stefanhepp/fancylights/firmware/MainController/src/ProjectorController.cpp

/*
 * @project     FancyController
 * @author      Stefan Hepp, stefan@stefant.org
 *
 * LED intensity and mode implementation.
 *
 * Copyright 2024 Stefan Hepp
 * License: GPL v3
 * See 'COPYRIGHT.txt' for copyright and licensing information.
 */
#include "ProjectorController.h"

#include <functional>

// for EVERY_N_MILLIS macro
#include <FastLED.h>

#include <commands.h>

#include "config.h"

HardwareSerial projectorSerial(UART_PROJECTOR);

const char *TOPIC_PROJECTOR_MODE = "mode";
const char *TOPIC_PROJECTOR_MOVE = "move";
const char *TOPIC_SCREEN_MOVE = "screen";
const char *TOPIC_PROJECTOR_POWER = "power";
const char *TOPIC_PROJECTOR_SWITCH = "endstop";

ProjectorController::ProjectorController(Settings &settings, MqttClient &mqttClient)
: mSettings(settings), mMqttClient(mqttClient)
{
}

void ProjectorController::mqttCallback(const char *key, const char* payload, unsigned int length)
{
    if (length == 0) {
        return;
    }
    if (strcmp(key, TOPIC_PROJECTOR_MODE) == 0) {
        ProjectorCommand mode;
        if (parseProjectorCommand(payload, mode)) {
            sendMode(mode, false);
        }
    }
    if (strcmp(key, TOPIC_PROJECTOR_MOVE) == 0) {
        LiftCommand move;
        if (parseLiftCommand(payload, move)) {
            moveProjector(move);
        }
    }
    if (strcmp(key, TOPIC_SCREEN_MOVE) == 0) {
        LiftCommand move;
        if (parseLiftCommand(payload, move)) {
            moveScreen(move);
        }
    }
}

void ProjectorController::subscribeCallback()
{
    mMqttClient.subscribe(MQS_PROJECTOR, TOPIC_PROJECTOR_MODE);
    mMqttClient.subscribe(MQS_PROJECTOR, TOPIC_PROJECTOR_MOVE);
    mMqttClient.subscribe(MQS_PROJECTOR, TOPIC_SCREEN_MOVE);
}

bool ProjectorController::isPowerChanging()
{
    return mPowerChangeTime > 0 && (millis() - mPowerChangeTime) < 1000; 
}

void ProjectorController::sendMode(ProjectorCommand mode, bool publish)
{
    bool modeChange = (mMode != mode);
    
    if ((mMode == ProjectorCommand::PROJECTOR_OFF) != (mode == ProjectorCommand::PROJECTOR_OFF)) {
        mPowerChangeTime = millis();
    }

    mMode = mode;

    // send command via SW UART to projector
    projectorSerial.write(ProjectorOpcode::POP_MODE);
    projectorSerial.write(mode);

    if (modeChange && mModeChangeCallback) {
        mModeChangeCallback(mode);
    }

    if (publish) {
        mMqttClient.publish(MQS_PROJECTOR, TOPIC_PROJECTOR_MODE, strProjectorCommand(mode));
    }
}

void ProjectorController::moveProjector(LiftCommand direction)
{
    projectorSerial.write( direction == LiftCommand::LIFT_UP ? ProjectorOpcode::POP_LOCK : ProjectorOpcode::POP_UNLOCK );
}

void ProjectorController::moveScreen(LiftCommand direction)
{
    mCntPulse = 5;
    if (direction == LiftCommand::LIFT_UP || direction == LiftCommand::LIFT_STOP) {
        digitalWrite(PIN_SCREEN_UP, HIGH);
    }
    if (direction == LiftCommand::LIFT_DOWN || direction == LiftCommand::LIFT_STOP) {
        digitalWrite(PIN_SCREEN_DOWN, HIGH);
    }
}

void ProjectorController::requestStatus()
{
    // Request status from projector controller
    projectorSerial.write(ProjectorOpcode::POP_STATUS);

    if (isPowerChanging()) {
        mDelayedStatusRequest = true;
    }
}

void ProjectorController::processSerialData(uint8_t data)
{
    mCommandData[mBufferSize++] = data;

    switch (mCommandData[0]) {
        case ProjectorOpcode::POP_STATUS:
            if (mBufferSize >= 2) {
                bool hasPowerStatus = ((mCommandData[1] >> 2) & 0x01);
                bool powerOn =        ((mCommandData[1] >> 1) & 0x01);
                bool switchState =    ( mCommandData[1]       & 0x01);

                if (hasPowerStatus) {
                    // check if the power status has changed, but ignore status immediately after powering on/off
                    if ( ((powerOn && mMode == PROJECTOR_OFF) || (!powerOn && mMode != PROJECTOR_OFF)) && !isPowerChanging()) {
                        mMode = powerOn ? PROJECTOR_ON : PROJECTOR_OFF;
                        if (mModeChangeCallback) {
                            mModeChangeCallback(mMode);
                        }
                        mMqttClient.publish(MQS_PROJECTOR, TOPIC_PROJECTOR_MODE, strProjectorCommand(mMode));
                    }

                    mMqttClient.publish(MQS_PROJECTOR, TOPIC_PROJECTOR_POWER, strBool(powerOn));
                }
                mMqttClient.publish(MQS_PROJECTOR, TOPIC_PROJECTOR_SWITCH, strBool(switchState));

                if (mStatusCallback) {
                    mStatusCallback(switchState, powerOn, hasPowerStatus, isPowerChanging());
                }

                // finish the command
                mBufferSize = 0;
            }
            break;
        default:
            // Ignore data if we received an unknown command
            mBufferSize = 0;
    }

    if (mBufferSize >= COM_BUF_SIZE) {
        // reset command buffer when full
        mBufferSize = 0;
    }
}

void ProjectorController::begin()
{
    using namespace std::placeholders;

    projectorSerial.begin(UART_SPEED_CONTROLLER, SERIAL_8N1, PIN_PR_RXD, PIN_PR_TXD);

    pinMode(PIN_SCREEN_UP, OUTPUT);
    pinMode(PIN_SCREEN_DOWN, OUTPUT);

    digitalWrite(PIN_SCREEN_UP, LOW);
    digitalWrite(PIN_SCREEN_DOWN, LOW);

    pinMode(PIN_WINCH_SWITCH, INPUT_PULLUP);
    pinMode(PIN_MOTOR_IN1, OUTPUT);
    pinMode(PIN_MOTOR_IN2, OUTPUT);

    digitalWrite(PIN_MOTOR_IN1, LOW);
    digitalWrite(PIN_MOTOR_IN2, LOW);

    auto callback = std::bind(&ProjectorController::mqttCallback, this, _1, _2, _3);
    auto subscribeCallback = std::bind(&ProjectorController::subscribeCallback, this);

    mMqttClient.registerClient(MQS_PROJECTOR, callback, subscribeCallback);
}

void ProjectorController::loop()
{
    // Process UART response
    while (projectorSerial.available()) {
        char data = projectorSerial.read();

        processSerialData(data);
    }

    // Send another status request after power up/down is finished
    if (mDelayedStatusRequest && !isPowerChanging()) {
        requestStatus();
        mDelayedStatusRequest = false;
    }

    EVERY_N_MILLISECONDS( 100 ) {
        if (mCntPulse > 0) {
            mCntPulse--;
            if (mCntPulse == 0) {
                digitalWrite(PIN_SCREEN_UP, LOW);
                digitalWrite(PIN_SCREEN_DOWN, LOW);
            }
        }
    }
}
