stefanhepp/fancylights/src/colortroll.c

/**
 * Project:   ColorTroll
 * File:      colortroll.c
 * Author:    Stefan Hepp <stefan@stefant.org>
 *
 * Copyright 2021 Stefan Hepp
 *
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
 * ColorTroll control board code for ColorTroll.
 *
 * Pinout:
 * - PortB:
 *   - PB0: 
 *   - PB1: 
 *   - PB2: 
 *   - PB3: 
 *   - PB4: 
 *   - PB5: 
 *   - PB6: 
 *   - PB7: 
 * - PortC:
 *   - PC0: 
 *   - PC1: 
 *   - PC2: 
 *   - PC3: 
 *   - PC4: 
 *   - PC5: 
 *   - PC6: 
 * - PortD:
 *   - PD0: 
 *   - PD1: 
 *   - PD2:
 *   - PD3:
 *   - PD4: 
 *   - PD5: 
 *   - PD6: 
 *   - PD7: 
 **/

// Define CPU clock speed and UART baud rate
#define F_CPU 1000000
#define BAUD  9600

#include <avr/io.h>
#include <avr/interrupt.h>
#include <avr/sleep.h>

// Baud rate calculation, delays
#include <util/setbaud.h>
#include <util/delay.h>

#include "uart.h"
#include "command.h"

#define SET_BIT(port,pin,value) \
    if (value) { \
	port |= _BV(pin);  \
    } else { \
	port &= ~_BV(pin); \
    }

void sleep(void)
{
    cli();

    // Only sleep it there is no input change since last read
    /*
    if (Last_input == PINB) {
	sleep_enable();
	sleep_bod_disable();
	sei();
	sleep_cpu();
	sleep_disable();
    } else {
	sei();
    }
    */
}

ISR(PCINT0_vect)
{
    // Register interrupt handler to wakeup CPU
}

int main()
{    
    // Disable interrupts
    cli();

    // Setup ports 
    /*
    init_io();

    // Configure UART
    init_uart();

    // Configure timer
    init_timer();

    init_switch(&SW_Livingroom);
    init_switch(&SW_Staircase);
    init_switch(&SW_Stair_Light);
    init_switch(&SW_Stair_Staircase);

    // Enable interrupts
    sei();

    while(1) {
	// Wait for any inputs
	//sleep();

	read_inputs();

	process_inputs();

	process_uart();

	write_outputs();

	// Debounce inputs
	_delay_ms(25);
    }
    */

    return 0;
}
