stefanhepp/fancylights/firmware/MainController/src/Settings.cpp

/*
 * @project     FancyLights
 * @author      Stefan Hepp, stefan@stefant.org
 *
 * Implementation of EEPROM access.
 *
 * Copyright 2024 Stefan Hepp
 * License: GPL v3
 * See 'COPYRIGHT.txt' for copyright and licensing information.
 */
#include "Settings.h"

#include <Preferences.h>

#include <commands.h>

static const char* PREF_NAMESPACE = "Prefs";

Preferences myPrefs;

Settings::Settings()
{
}

void Settings::begin()
{
    myPrefs.begin(PREF_NAMESPACE);
}

bool Settings::isLampEnabled()
{
    return myPrefs.getUChar("lampOn", 0);
}

bool Settings::isLEDStripEnabled()
{
    return myPrefs.getUChar("LEDOn", 0);
}

void Settings::setLampEnabled(bool enabled)
{
    myPrefs.putUChar("lampOn", enabled);
    mChanged = true;
}

void Settings::setLEDStripEnabled(bool enabled)
{
    myPrefs.putUChar("LEDOn", enabled);
    mChanged = true;
}


RGBMode Settings::rgbMode()
{
    return (RGBMode) myPrefs.getUChar("rgbMode", RGBMode::RGB_ON);
}

void Settings::setRGBMode(RGBMode mode)
{
    myPrefs.putUChar("rgbMode", mode);
    mChanged = true;
}


uint8_t Settings::intensity()
{
    return myPrefs.getUChar("intensity", 255);
}

void Settings::setIntensity(uint8_t value)
{
    myPrefs.putUChar("intensity", value);
    mChanged = true;
}

uint8_t Settings::dimmedIntensity()
{
    return myPrefs.getUChar("dimIntensity", 40);
}

void Settings::setDimmedIntensity(uint8_t value)
{
    myPrefs.putUChar("dimIntensity", value);
    mChanged = true;
}


CHSV Settings::getHSV()
{
    uint8_t hsv[3];
    CHSV chsv;

    myPrefs.getBytes("hsv", hsv, sizeof(hsv));
    chsv.setHSV(hsv[0], hsv[1], hsv[2]);

    return chsv;
}

void Settings::setHSV(uint8_t hue, uint8_t saturation, uint8_t value)
{
    uint8_t hsv[3] = {hue, saturation, value};
    myPrefs.putBytes("hsv", hsv, sizeof(hsv));
    mChanged = true;
}

String Settings::getWiFiSSID()
{
    return myPrefs.getString("wifiSSID", "");
}

String Settings::getWiFiPassword()
{
    return myPrefs.getString("wifiPW", "");
}

void Settings::setWiFiAccess(const char *ssid, const char *password)
{
    myPrefs.putString("wifiSSID", ssid);
    myPrefs.putString("wifiPW", password);
}

String Settings::getHostname()
{
    return myPrefs.getString("hostname", "fancyled.home");
}

void Settings::setHostname(const char *hostname)
{
    myPrefs.putString("hostname", hostname);
}

String Settings::getMQTTServer()
{
    return myPrefs.getString("mqttServer", "homectl.home");
}

String Settings::getMQTTTopic()
{
    return myPrefs.getString("mqttTopic", "leds");
}

uint16_t Settings::getMQTTPort()
{
    return myPrefs.getUShort("mqttPort", 1883);
}

void Settings::setMQTTServer(const char *server, uint16_t port, const char *topic)
{
    myPrefs.putString("mqttServer", server);
    myPrefs.putUShort("mqttPort", port);
    myPrefs.putString("mqttTopic", topic);
}

String Settings::getMQTTClientID()
{
    return myPrefs.getString("mqttClient", "fancyleds");
}

String Settings::getMQTTUsername()
{
    return myPrefs.getString("mqttUser");
}

String Settings::getMQTTPassword()
{
    return myPrefs.getString("mqttPass");
}

void Settings::setMQTTClient(const char *clientId, const char *username, const char *password)
{
    myPrefs.putString("mqttClient", clientId);
    myPrefs.putString("mqttUser", username);
    myPrefs.putString("mqttPass", password);
}
